victorhalla/hasf/src/images/HASF-Cover.png

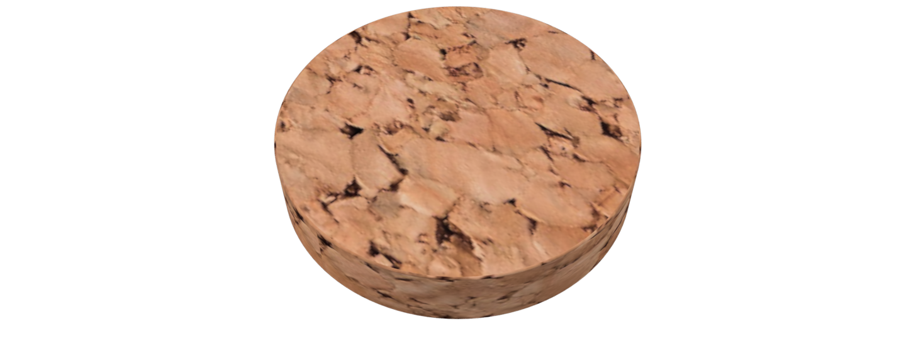
src/images/HASF-Cover.png
