victorhalla/hasf/src/images/HASF-Nest.png

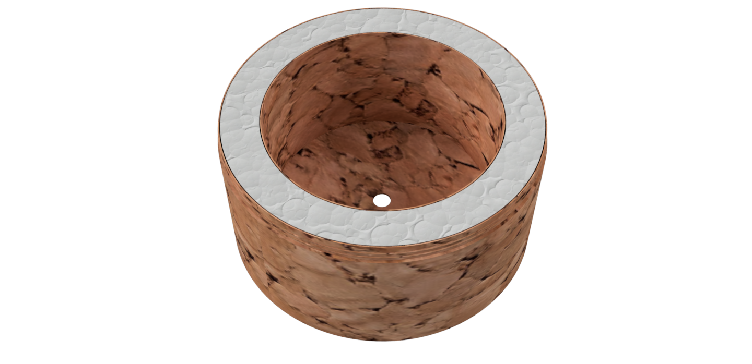
src/images/HASF-Nest.png
