victorhalla/hasf/src/images/HASF-Overnest.png

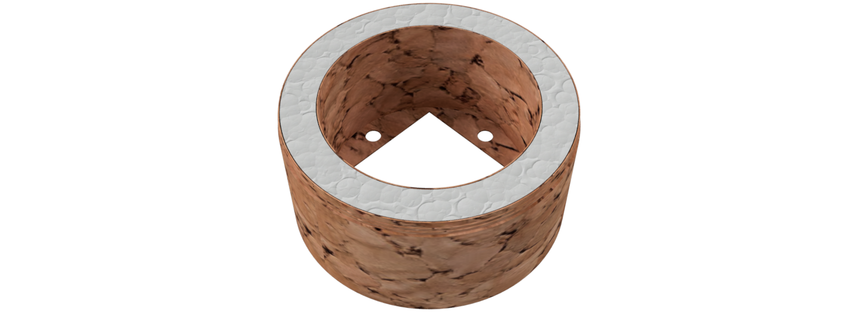
src/images/HASF-Overnest.png
