victorhalla/hasf/src/images/HASF-SectionView.png

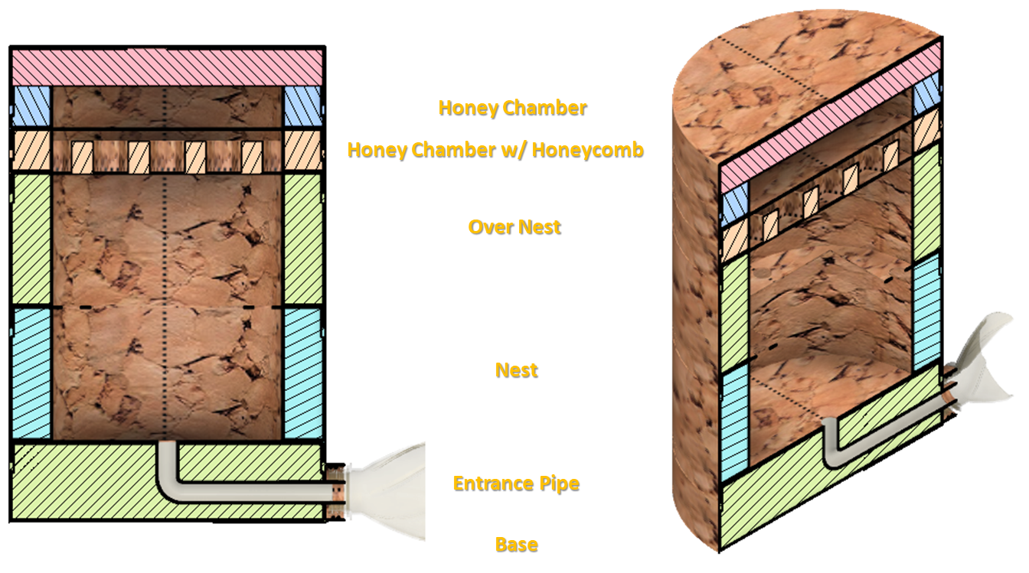
src/images/HASF-SectionView.png
