victorhalla/hasf/src/images/HASF-SectionViewAngle.png

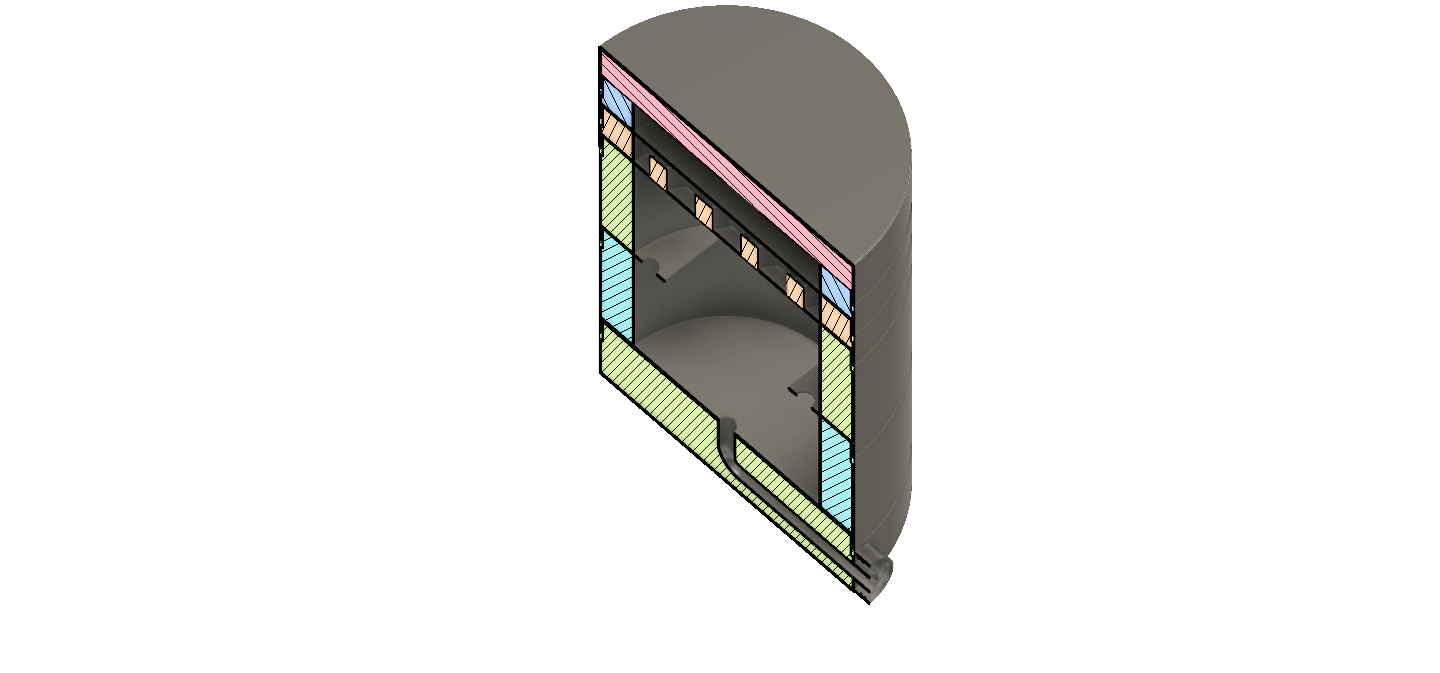
src/images/HASF-SectionViewAngle.png
