victorhalla/hasf/src/images/HASFv2-BASE-VENTILATION-SECTION-YZ.png

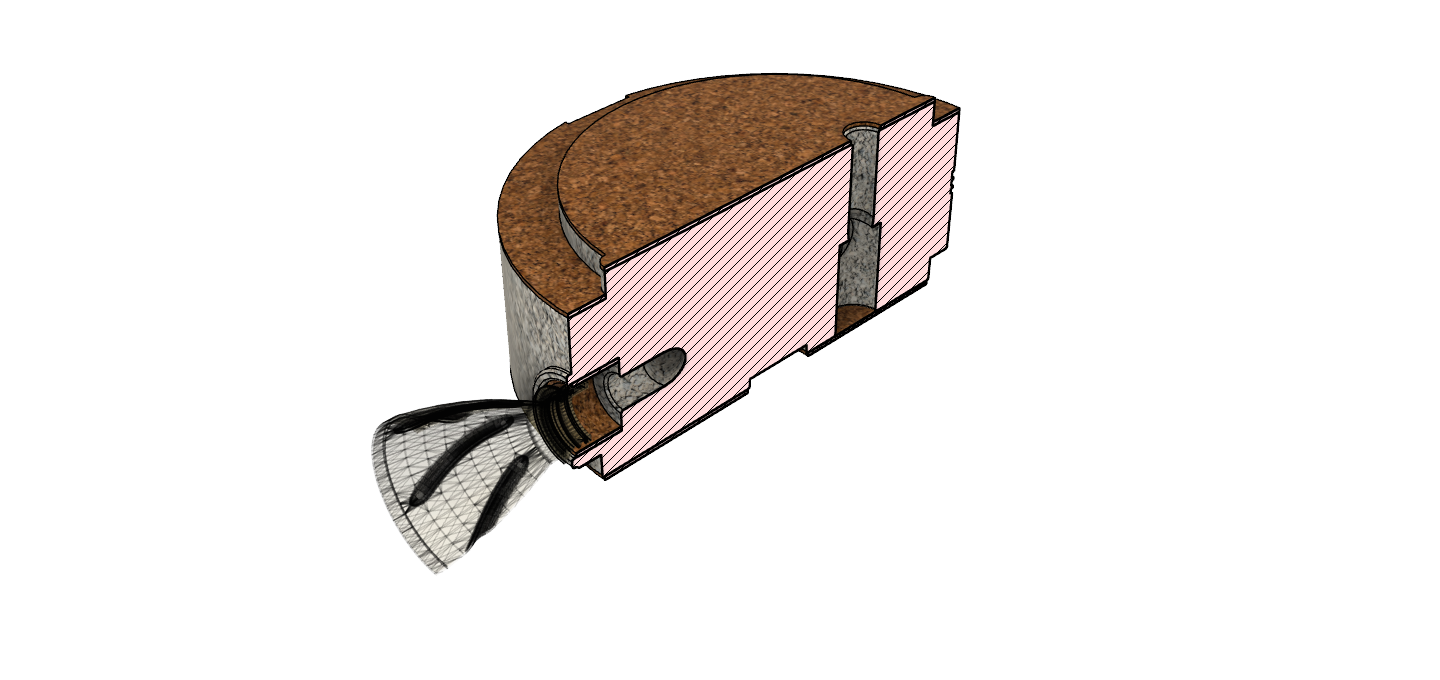
src/images/HASFv2-BASE-VENTILATION-SECTION-YZ.png
