victorhalla/hasf/src/images/HASFv2-COVER-SECTION-YZ.png

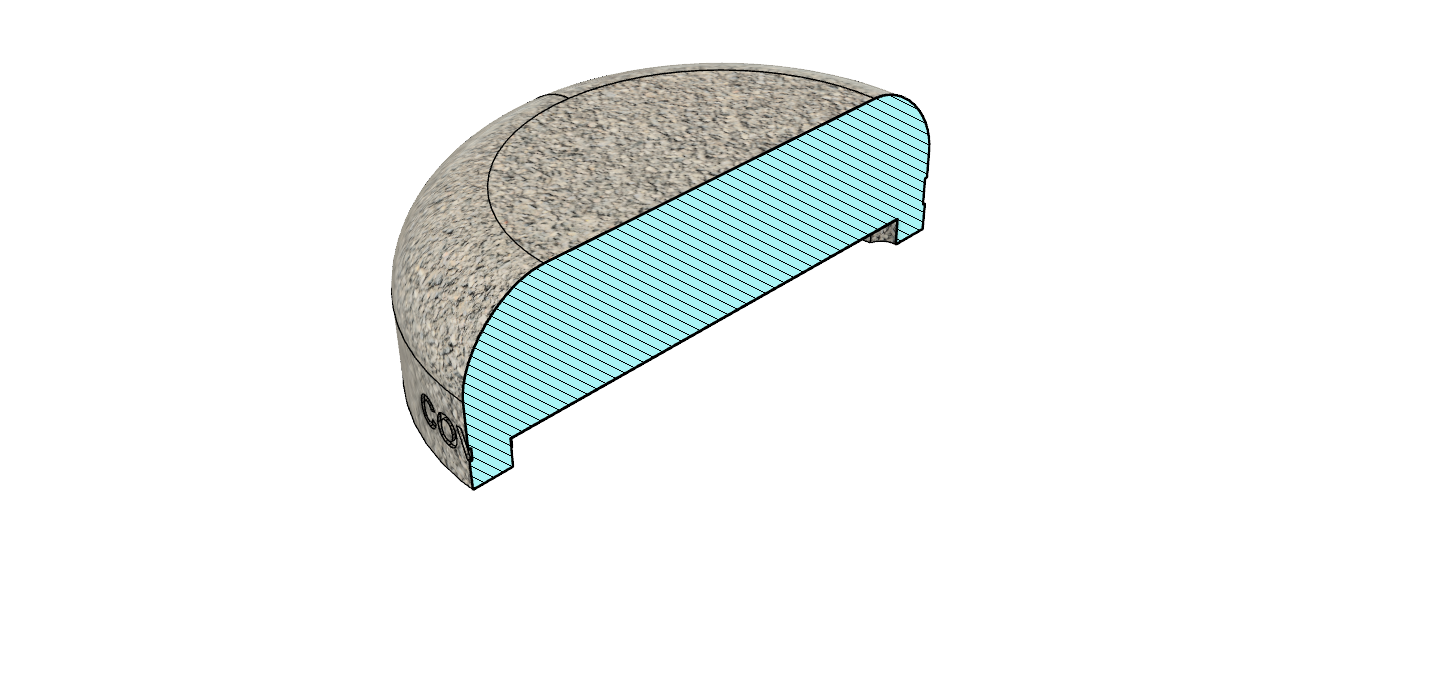
src/images/HASFv2-COVER-SECTION-YZ.png
