victorhalla/hasf/src/images/HASFv2-COVER-VENTILATION.png

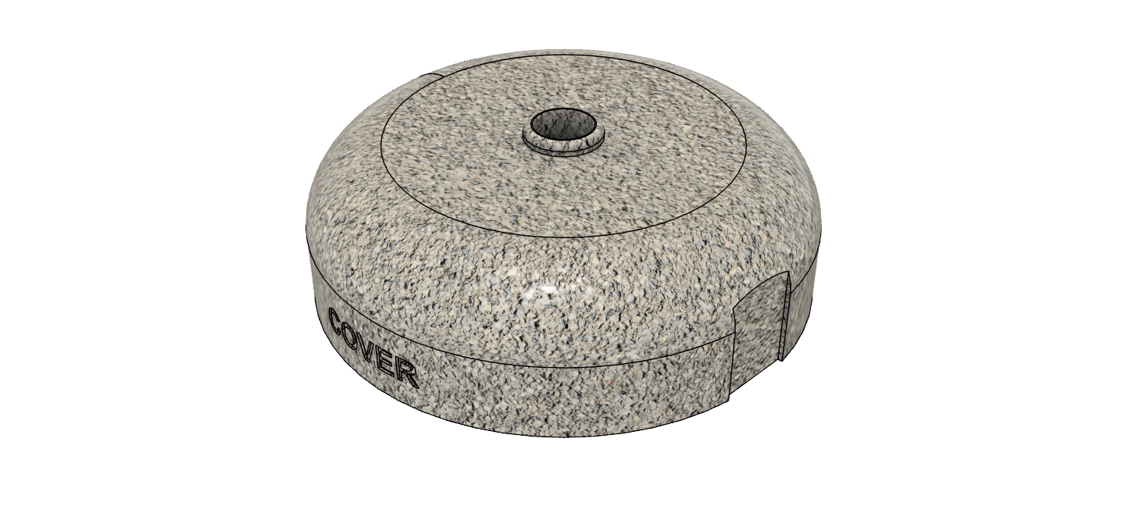
src/images/HASFv2-COVER-VENTILATION.png
