victorhalla/hasf/src/images/HASFv2-HONEY-SECTION-YZ.png

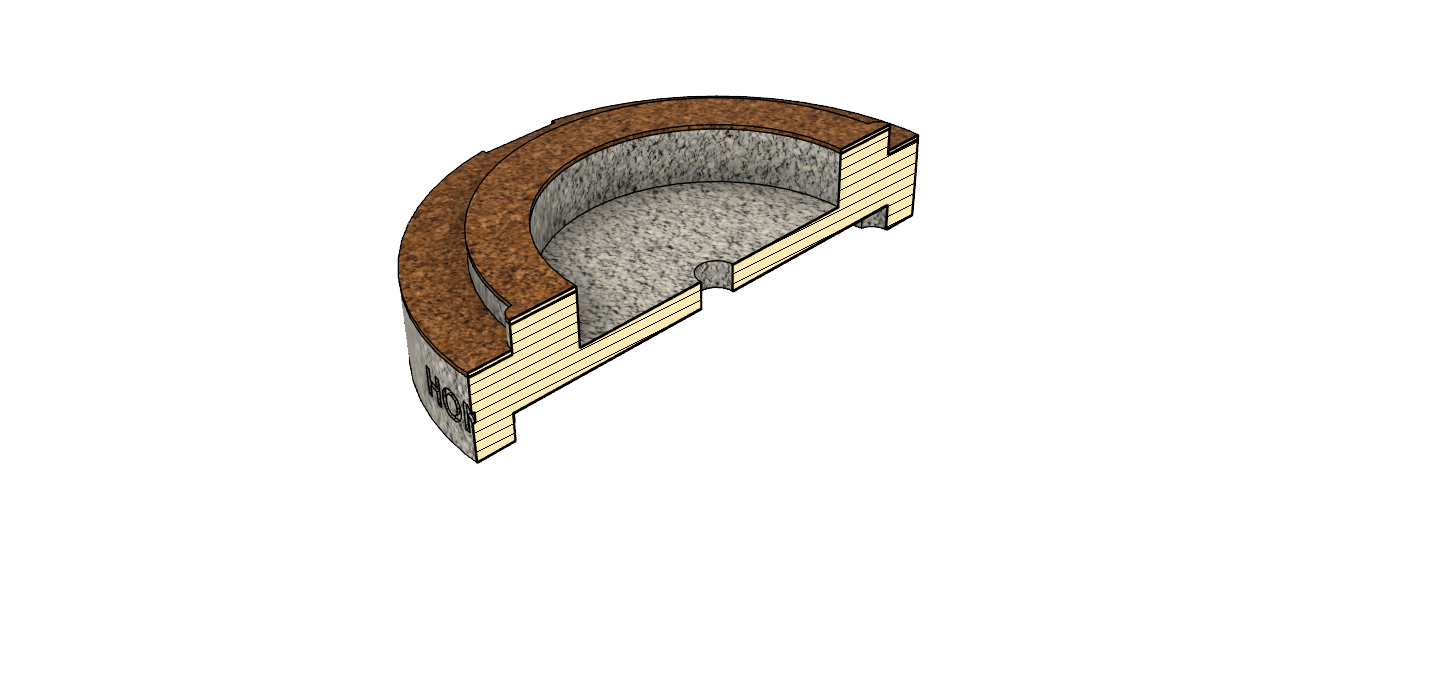
src/images/HASFv2-HONEY-SECTION-YZ.png
