victorhalla/hasf/src/images/HASFv2-HONEY.png

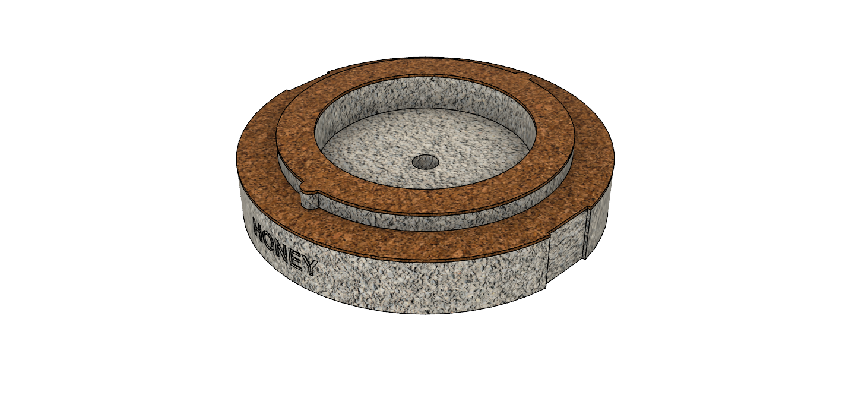
src/images/HASFv2-HONEY.png
