victorhalla/hasf/src/images/HASFv2-NEST-BOTTON.png

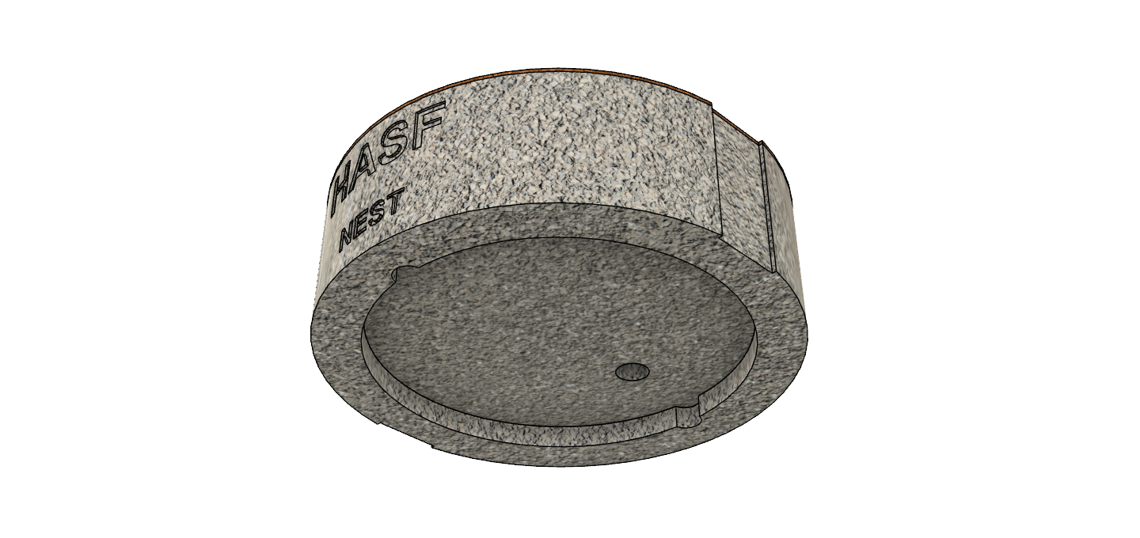
src/images/HASFv2-NEST-BOTTON.png
