victorhalla/hasf/src/images/HASFv2-NEST.png

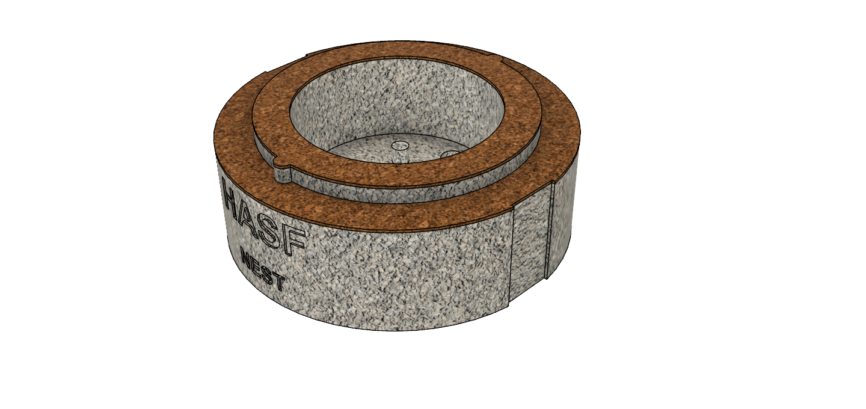
src/images/HASFv2-NEST.png
