victorhalla/hasf/src/images/HASFv2-OVERNEST-SECTION-YX.png

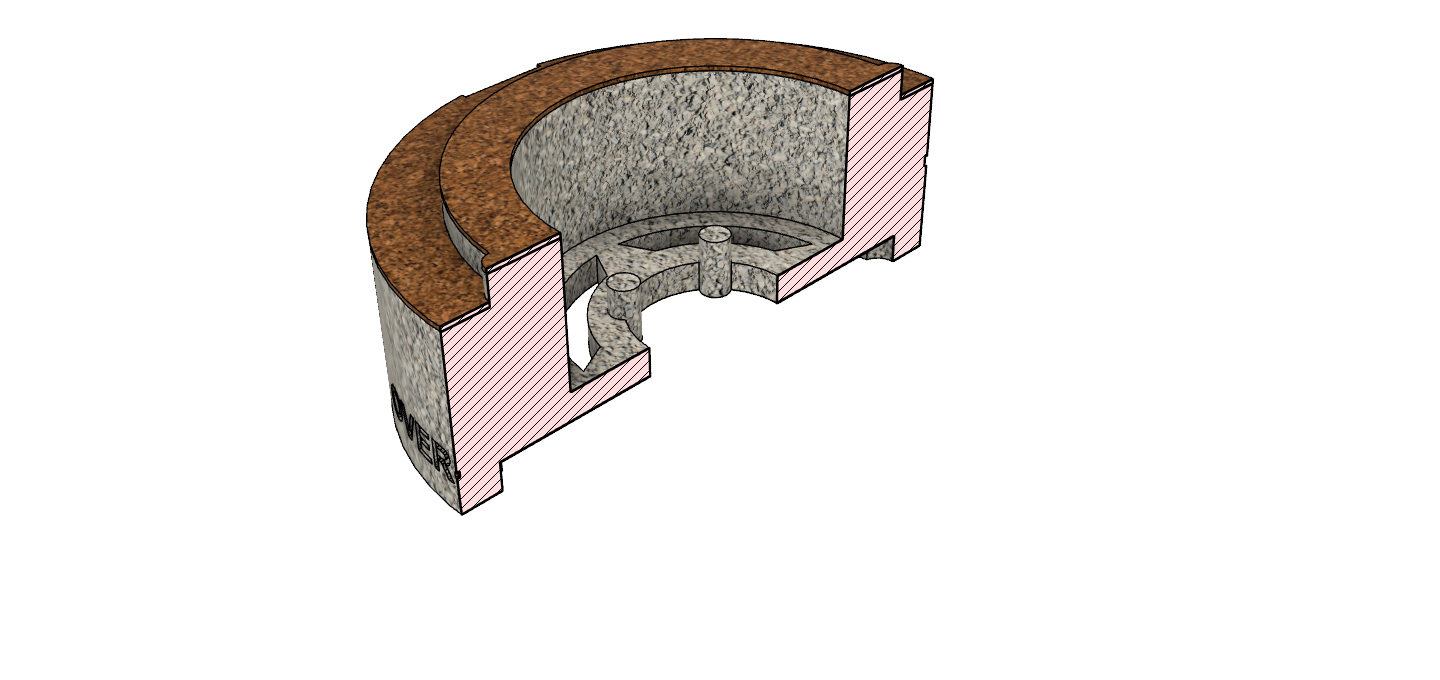
src/images/HASFv2-OVERNEST-SECTION-YX.png
