victorhalla/hasf/src/images/HASFv2-OVERNEST.png

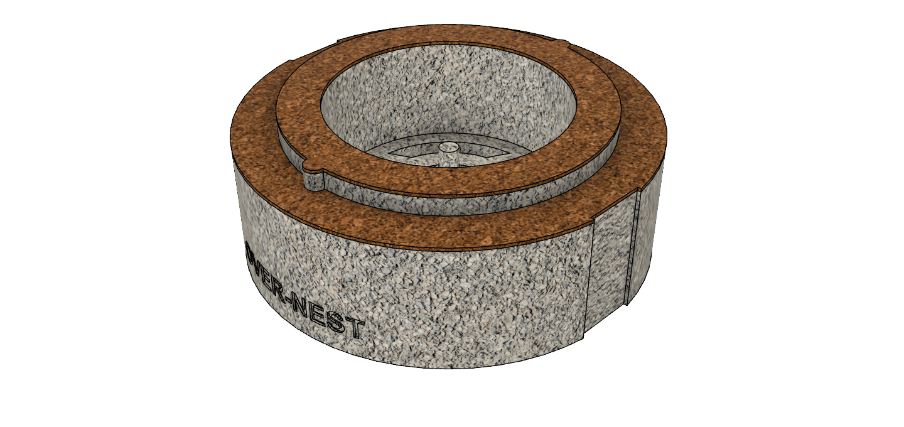
src/images/HASFv2-OVERNEST.png
