victorhalla/hasf/src/images/HASFv2-ROOF-SECTION-YZ.png

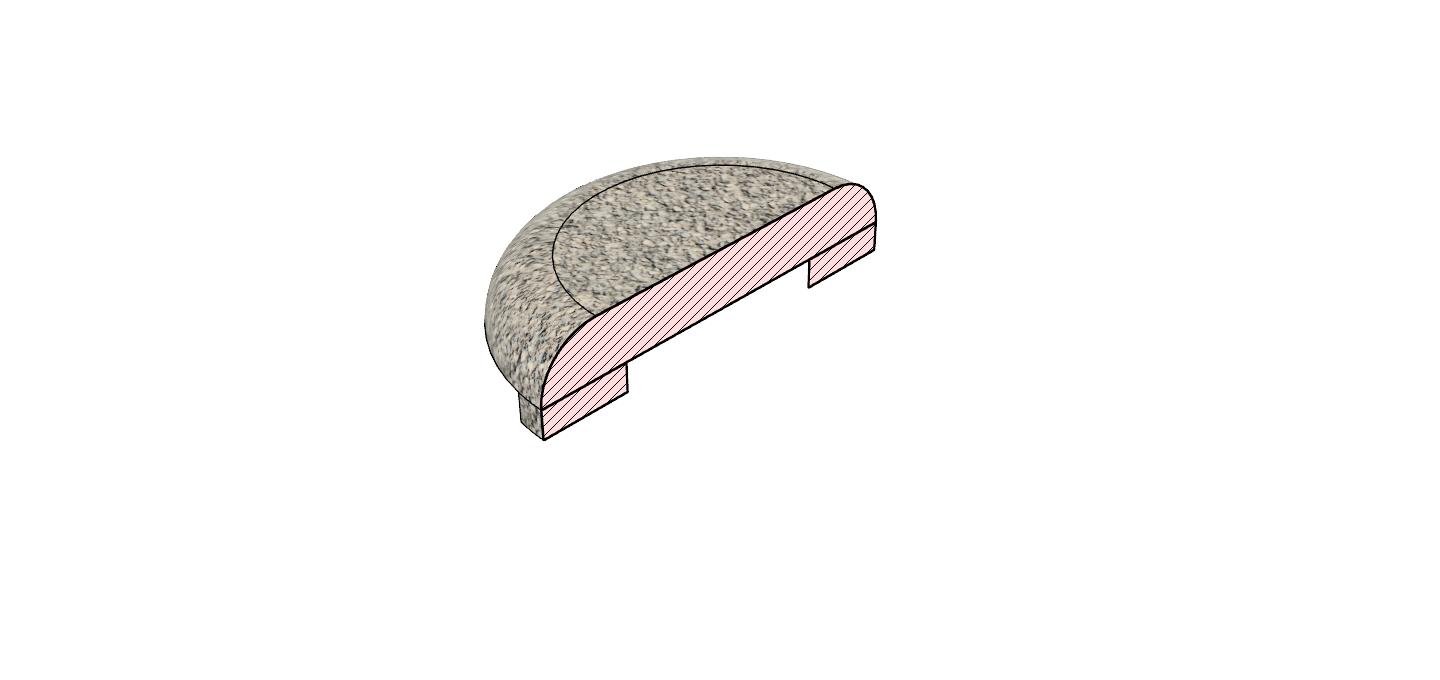
src/images/HASFv2-ROOF-SECTION-YZ.png
