victorhalla/hasf/src/stl/A/HASFv2-A-HONEY.stl

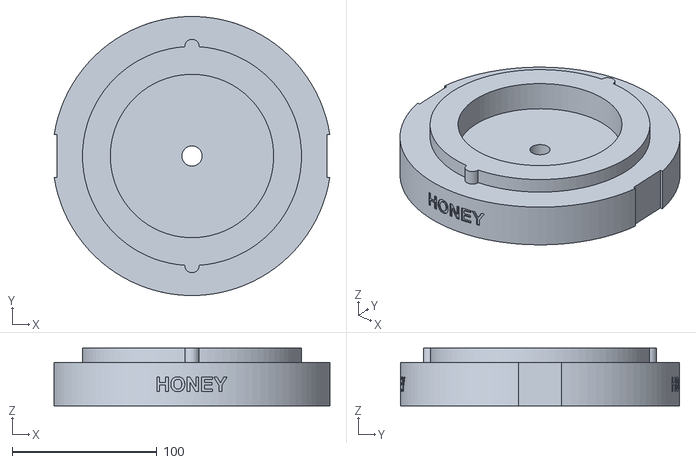
[picture p56: CAD file, 2022-07-22]
src/stl/A/HASFv2-A-HONEY.stl
190.7 x 193.0 x 40.0
