victorhalla/hasf/src/stl/B/HASFv2-B-BASE-VENTILATION-ELETRONICS.stl

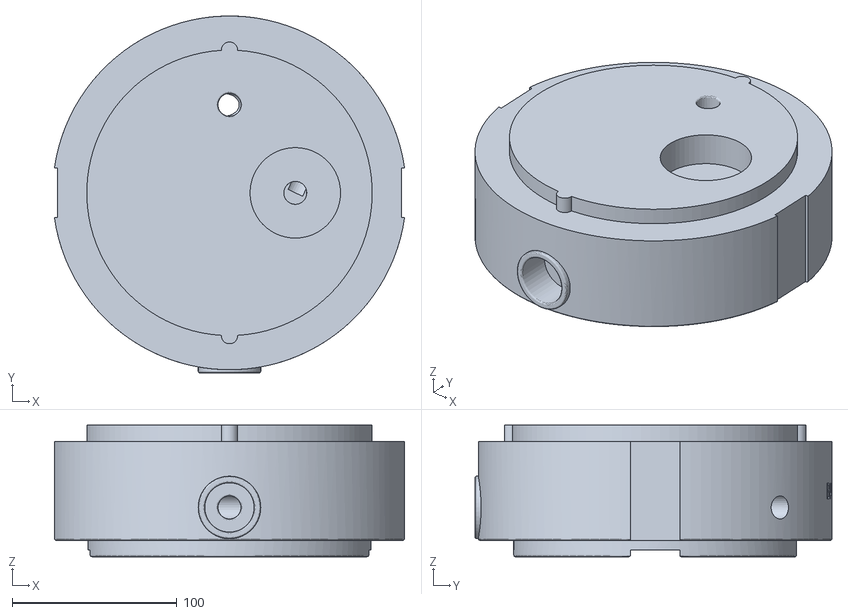
[picture p57: CAD file, 2022-08-01]
src/stl/B/HASFv2-B-BASE-VENTILATION-ELETRONICS.stl
212.9 x 217.0 x 80.0
