victorhalla/hasf/src/stl/A/HASFv2-A-NEST.stl

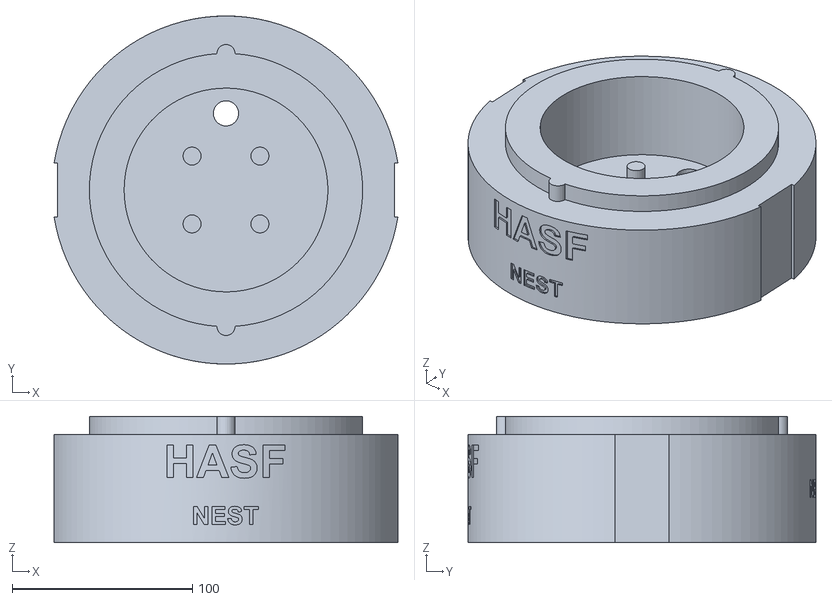
[picture p58: CAD file, 2022-07-22]
src/stl/A/HASFv2-A-NEST.stl
190.7 x 193.0 x 70.0
