victorhalla/hasf/src/stl/B/HASFv2-B-ROOF.stl

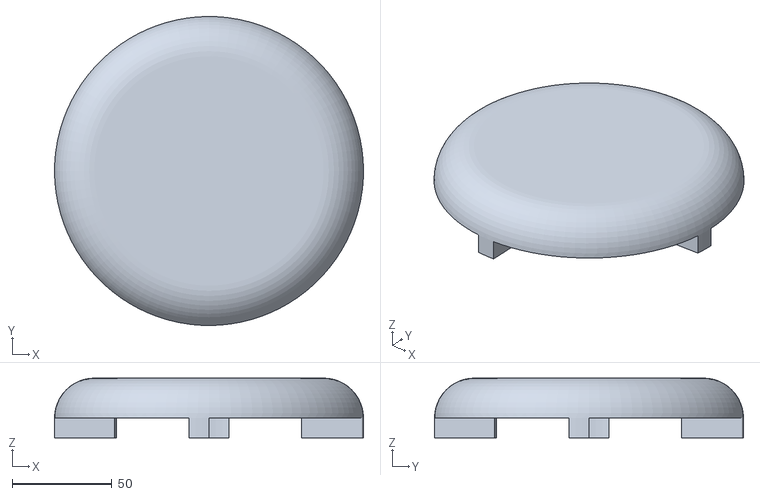
[picture p59: CAD file, 2022-08-01]
src/stl/B/HASFv2-B-ROOF.stl
155.0 x 155.0 x 30.0
