victorhalla/hasf/src/stl/A/HASFv2-A-COVER.stl

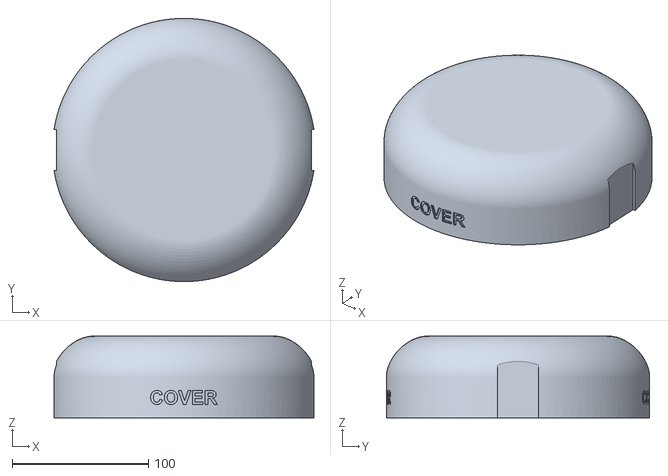
[picture p60: CAD file, 2022-07-22]
src/stl/A/HASFv2-A-COVER.stl
190.7 x 193.0 x 60.0
