victorhalla/hasf/src/stl/A/HASFv2-A-OVERNEST.stl

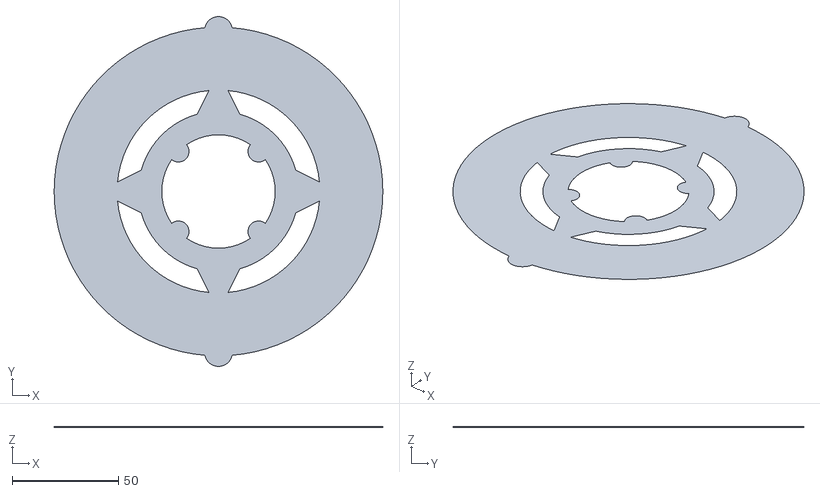
[picture p61: CAD file, 2022-07-22]
src/stl/A/HASFv2-A-OVERNEST.stl
154.5 x 164.5 x 0.1
