victorhalla/hasf/src/stl/B/HASFv2-B-SUPER.PT-BR.stl

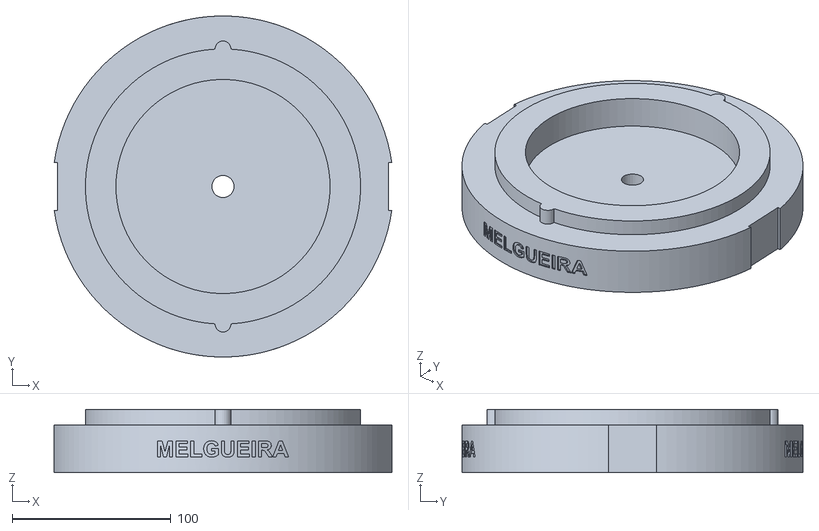
[picture p62: CAD file, 2022-08-01]
src/stl/B/HASFv2-B-SUPER.PT-BR.stl
212.9 x 215.0 x 40.0
