victorhalla/hasf/src/stl/A/HASFv2-A-BASE-SEAL-BASE-VENTILATION.stl

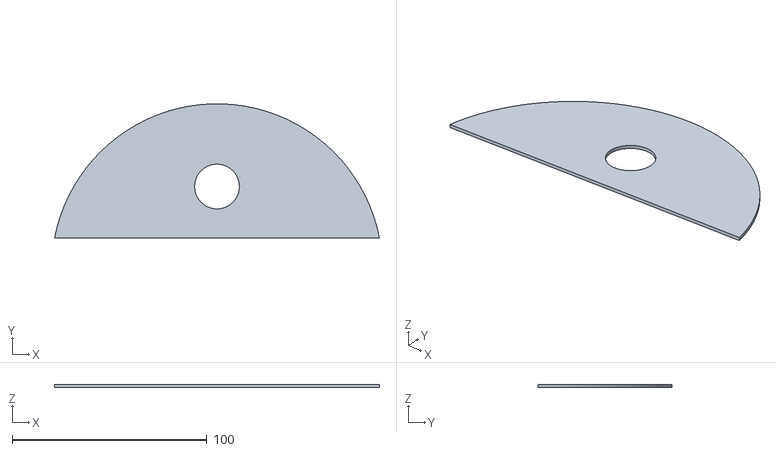
[picture p63: CAD file, 2022-07-22]
src/stl/A/HASFv2-A-BASE-SEAL-BASE-VENTILATION.stl
167.0 x 69.0 x 1.60
