victorhalla/hasf/src/stl/A/HASFv2-A-COVER-SEPARATOR-ACETATE.stl

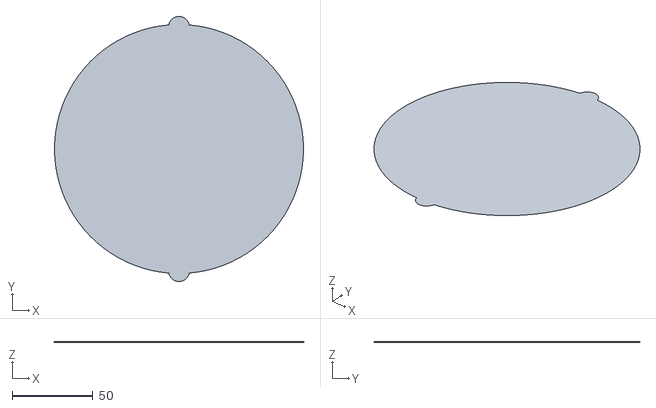
[picture p64: CAD file, 2022-07-22]
src/stl/A/HASFv2-A-COVER-SEPARATOR-ACETATE.stl
154.5 x 164.5 x 0.1
