victorhalla/hasf/src/stl/B/HASFv2-B-OVERNEST.stl

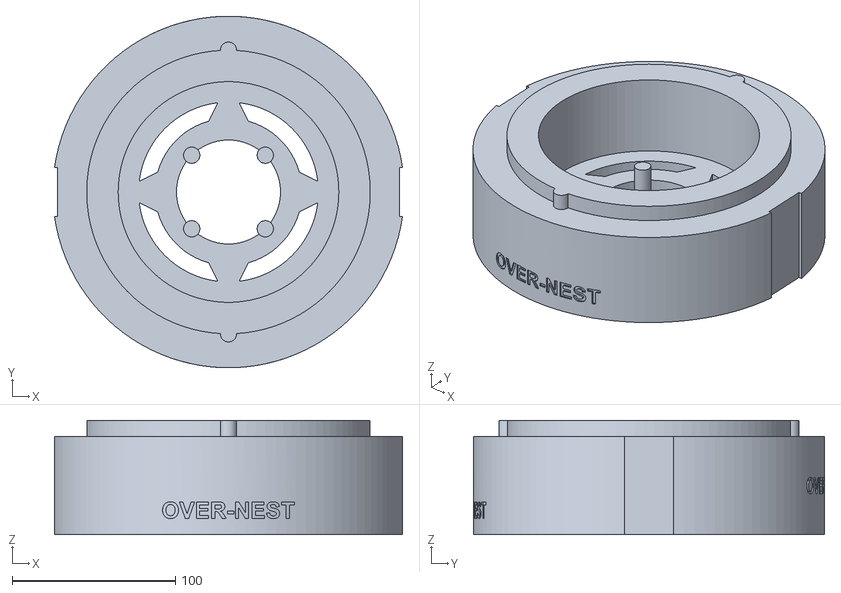
[picture p65: CAD file, 2022-08-01]
src/stl/B/HASFv2-B-OVERNEST.stl
212.9 x 215.0 x 70.0
