victorhalla/hasf/src/stl/A/HASFv2-A-SEAL-INTERNAL.stl

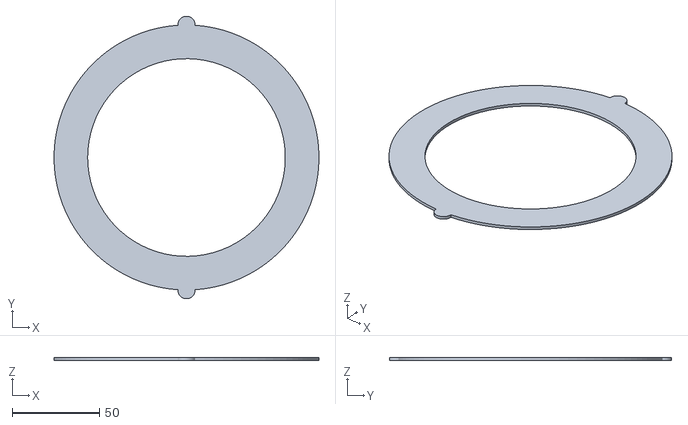
[picture p66: CAD file, 2022-07-22]
src/stl/A/HASFv2-A-SEAL-INTERNAL.stl
151.5 x 161.4 x 1.60
