victorhalla/hasf/src/stl/A/HASFv2-A-BASE-SEAL-BASE.stl

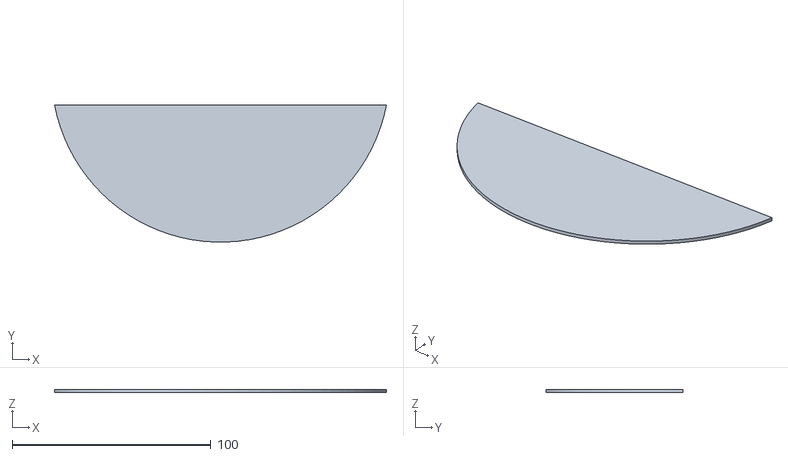
[picture p67: CAD file, 2022-07-22]
src/stl/A/HASFv2-A-BASE-SEAL-BASE.stl
167.0 x 69.0 x 1.60
