victorhalla/hasf/src/stl/A/HASFv2-A-COVER-VENTILATION.stl

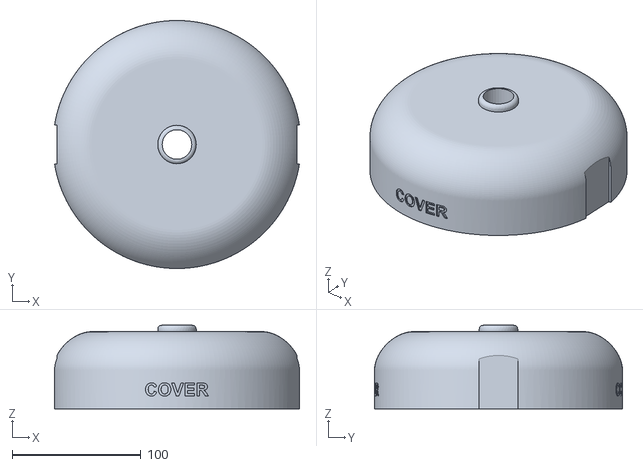
[picture p68: CAD file, 2022-07-22]
src/stl/A/HASFv2-A-COVER-VENTILATION.stl
190.7 x 193.0 x 65.0
